Rkashif1/Design-and-Evaluation-of-an-Adaptive-FPGA-Board-with-Modular-Connector-Interface/Practice_Works KICAD/Refrence Pictures/5V_REGULATOR PCB.jpg

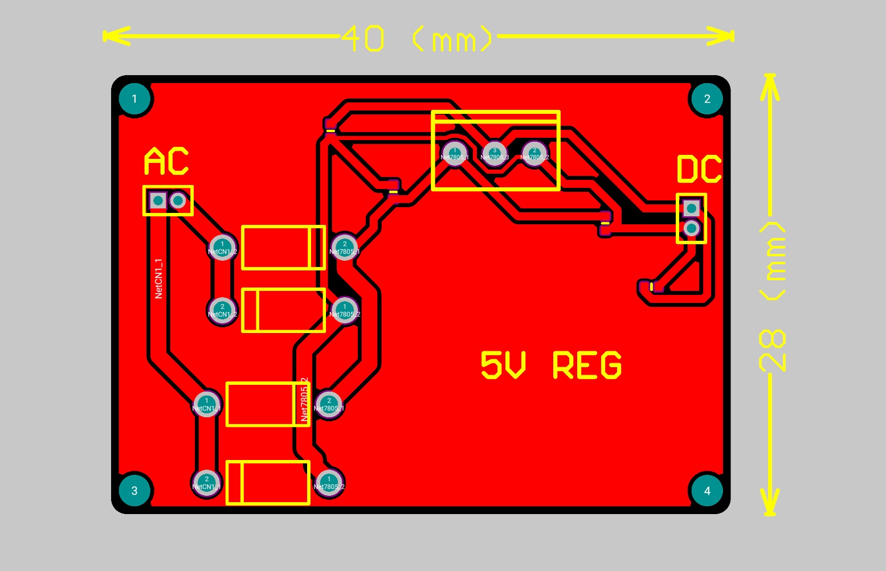
Practice_Works KICAD/Refrence Pictures/5V_REGULATOR PCB.jpg
