Rkashif1/Design-and-Evaluation-of-an-Adaptive-FPGA-Board-with-Modular-Connector-Interface/Practice_Works KICAD/Refrence Pictures/FPGA_BOARD PCB 3D.jpg

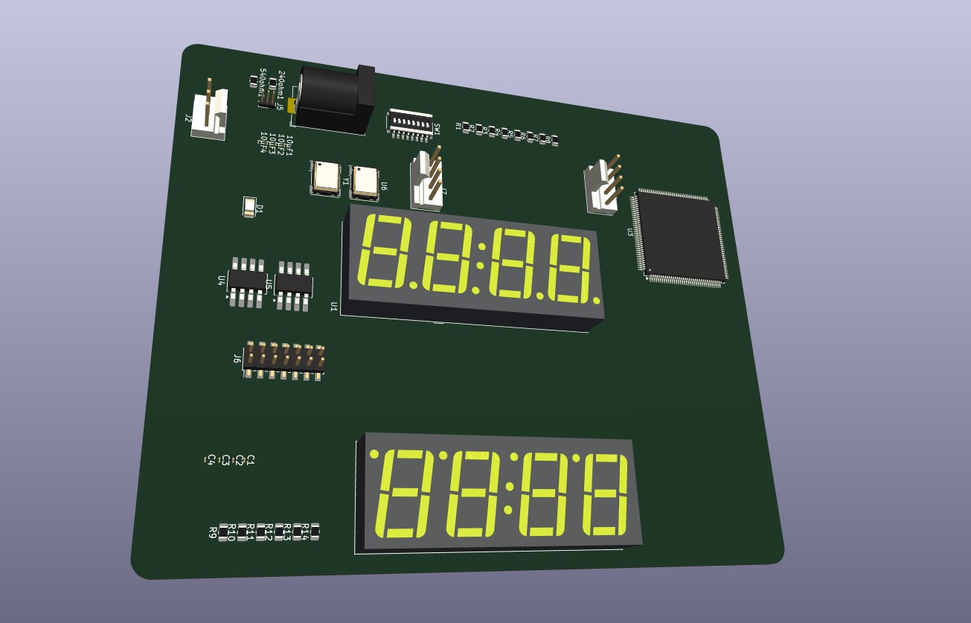
Practice_Works KICAD/Refrence Pictures/FPGA_BOARD PCB 3D.jpg
