Rkashif1/Design-and-Evaluation-of-an-Adaptive-FPGA-Board-with-Modular-Connector-Interface/Practice_Works KICAD/Refrence Pictures/FPGA_BOARD SCHEMATIC_03.jpg

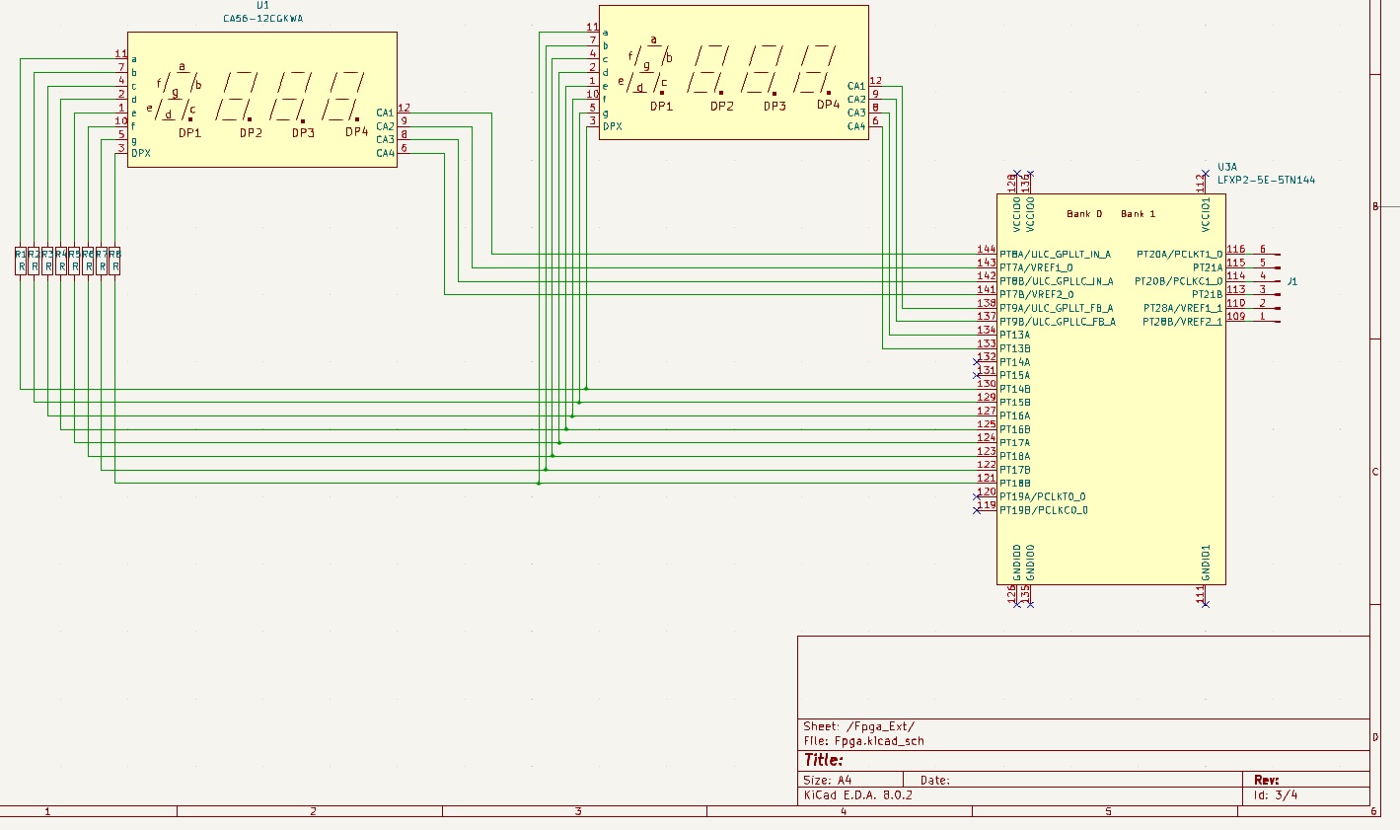
Practice_Works KICAD/Refrence Pictures/FPGA_BOARD SCHEMATIC_03.jpg
