Rkashif1/Design-and-Evaluation-of-an-Adaptive-FPGA-Board-with-Modular-Connector-Interface/Project_Refrence_Images/Architecture/Block_Diagram.png

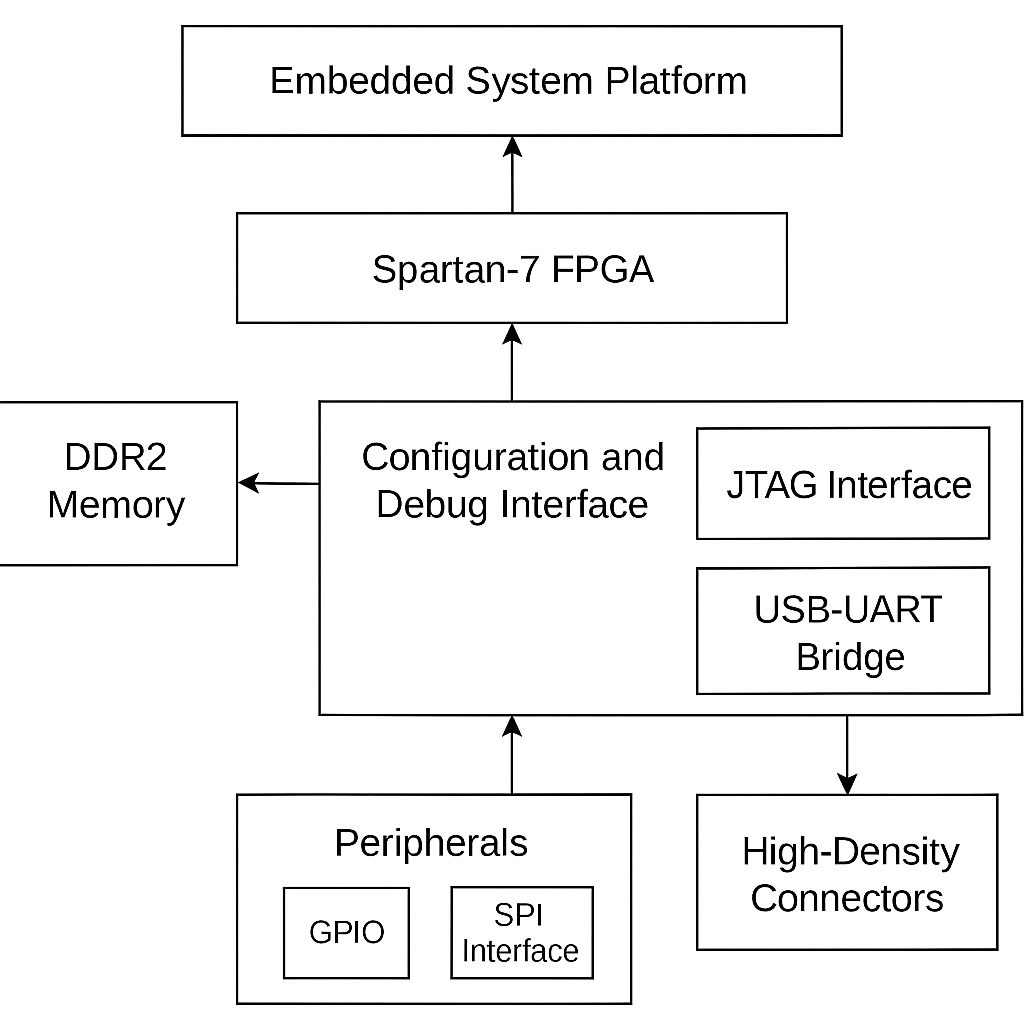
Project_Refrence_Images/Architecture/Block_Diagram.png
