Rkashif1/Design-and-Evaluation-of-an-Adaptive-FPGA-Board-with-Modular-Connector-Interface/Project_Refrence_Images/Floor_Planning/Floor_Plan.png

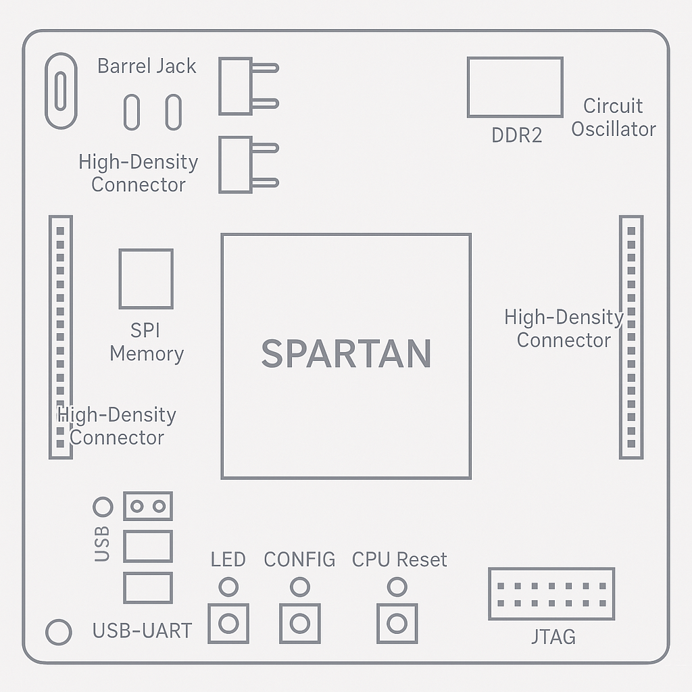
Project_Refrence_Images/Floor_Planning/Floor_Plan.png
