Rkashif1/Design-and-Evaluation-of-an-Adaptive-FPGA-Board-with-Modular-Connector-Interface/Project_Refrence_Images/PCB/DRC check.jpg

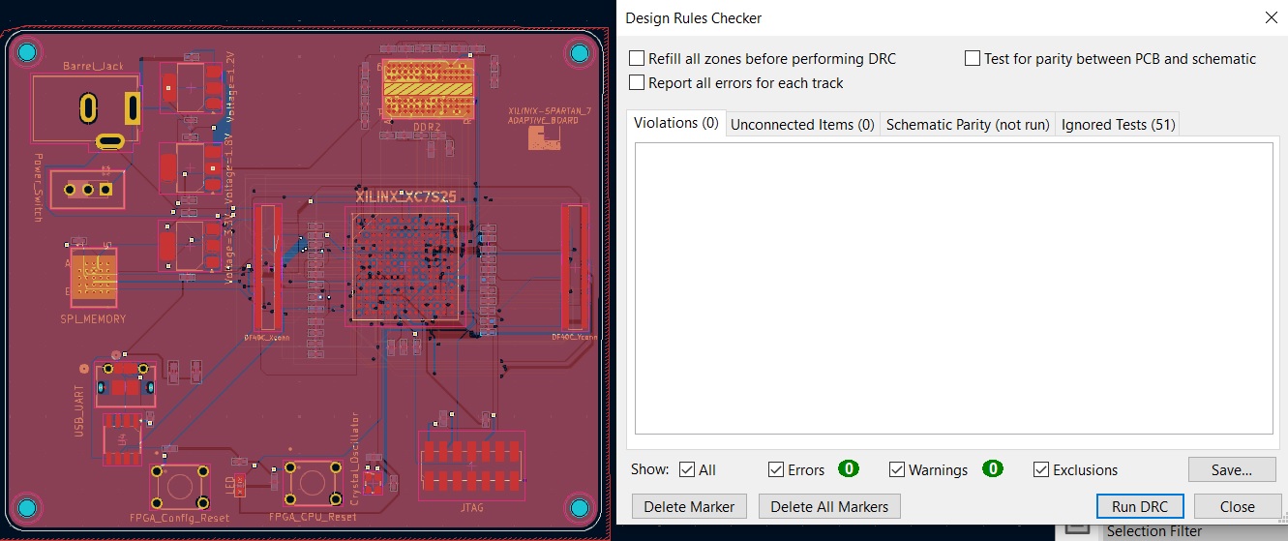
Project_Refrence_Images/PCB/DRC check.jpg
