Rkashif1/Design-and-Evaluation-of-an-Adaptive-FPGA-Board-with-Modular-Connector-Interface/Project_Refrence_Images/Schematics/Xilinx_JTAG.jpg

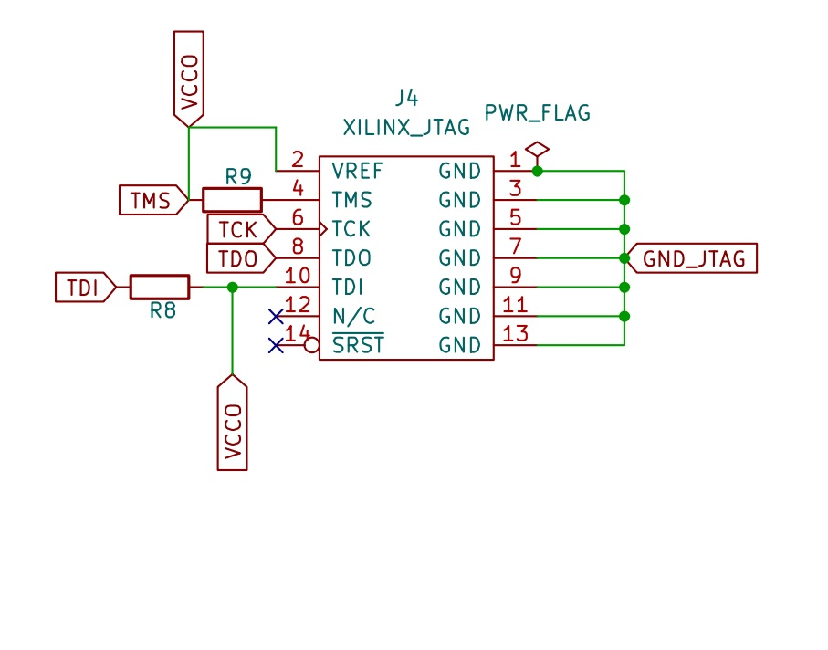
Project_Refrence_Images/Schematics/Xilinx_JTAG.jpg
